LieBtrau/ohis-ht-interface/simulations/smartphone.asc

C1: cap; 1µ
C2: cap; 10n
R1: res; 33k
R2: res; 1k
R4: res; 33k
V1: voltage; SINE(0 1.41 1k); AC 1.41
Named nets: 0, out
.ac dec 100 1 100k
Audio range = 300Hz to 3kHz
max. 1Vrms out (0dBV) for OHIS headphone
;tran 1
Mic-IN
