LieBtrau/ohis-ht-interface/simulations/FT-65E.asc

C1: cap; 100µ
C2: cap; 100n
R1: res; 39
R2: res; 64
R3: res; 10k
R4: res; 10k
V1: voltage; SINE(1.85 2.32 1k); AC 2.32
Named nets: 0, out
.ac dec 100 10 100k
Audio range = 300Hz to 3kHz
max. 1Vrms out (0dBV) for OHIS headphone
;tran 1
Headphone (8ohm to 64ohm)
